SudoChii/MakoReactor/notebooks/artifacts/pico_holder.stl

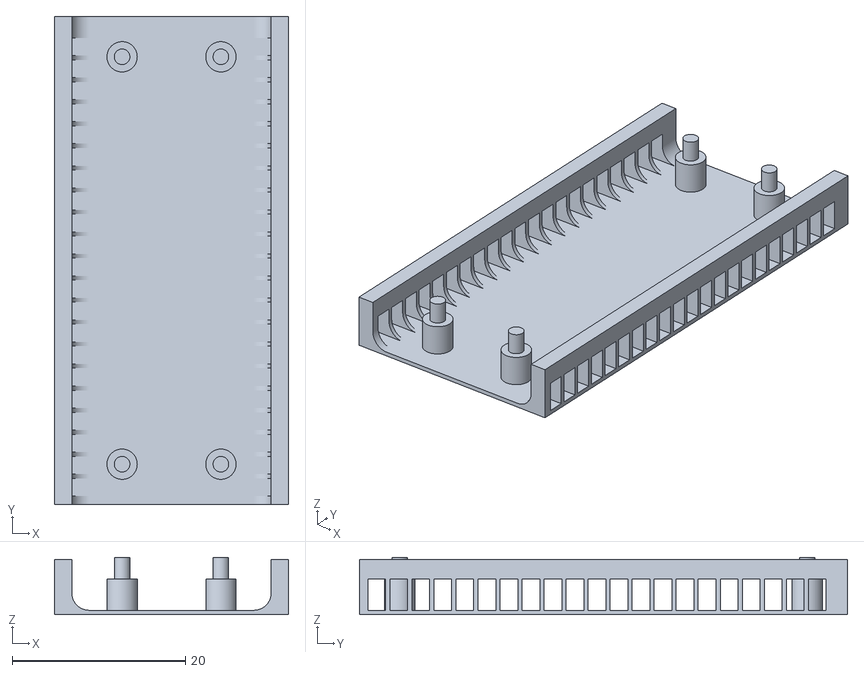
[picture p17: CAD file, 2026-07-18]
notebooks/artifacts/pico_holder.stl
27.0 x 56.3 x 6.60
