SudoChii/MakoReactor/notebooks/mako1_fgc/layer4.dxf

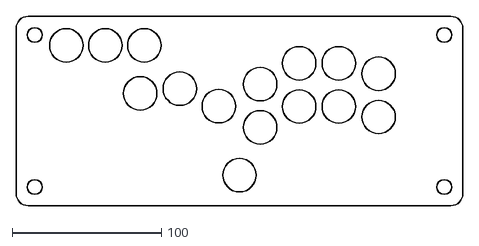
[picture p18: CAD file, 2026-07-18]
notebooks/mako1_fgc/layer4.dxf
299.7 x 127.0
