SudoChii/MakoReactor/notebooks/artifacts/keebcap_faceplate.dxf

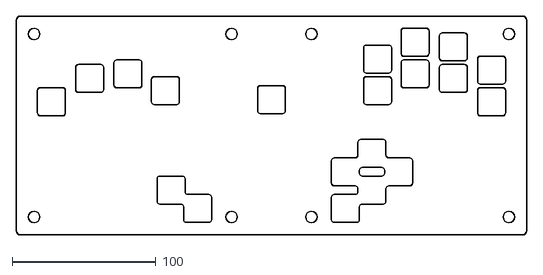
[picture p19: CAD file, 2026-07-18]
notebooks/artifacts/keebcap_faceplate.dxf
355.6 x 152.4
