SudoChii/MakoReactor/notebooks/artifacts/dowel.dxf

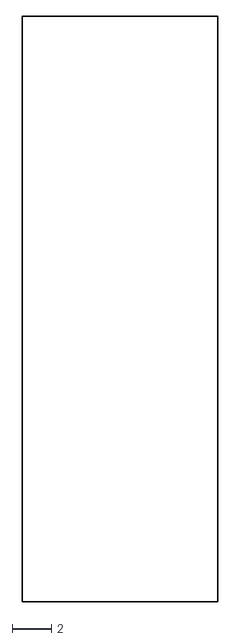
[picture p20: CAD file, 2026-07-18]
notebooks/artifacts/dowel.dxf
10.0 x 30.0
