SudoChii/MakoReactor/notebooks/artifacts/bottom.dxf

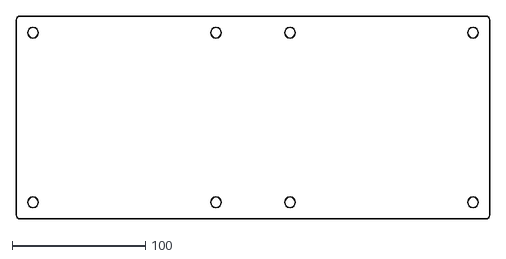
[picture p21: CAD file, 2026-07-18]
notebooks/artifacts/bottom.dxf
355.6 x 152.4
